ExcessiveOverkill/PCB-business-cards/STM32/opensauce 2024/opensauce2024/Core/Inc/imageData.h

#define IMAGE_DATA {0, 0, 0, 0, 0, 0, 0, 8386560, 8391680, 16778752, 16778752, 16778752, 536870910, 1073741823, 1610612743, 3221225475, 2147483651, 2147483651, 2179989507, 2214068350, 2216427584, 2215379008, 2215379008, 2215379008, 2215379070, 2240544775, 2240544771, 2240544771, 1166802947, 629932035, 495976446, 34078720, 32505856, 0, 0, 0, 0, 0, 0, 0, 0, 7340032, 7340032, 7340032, 25952256, 25952256, 110231552, 110231552, 77692928, 138932224, 135794432, 136315072, 138412080, 138412044, 142606338, 142606337, 83886081, 83886081, 50331649, 16777246, 16777232, 16777232, 16777248, 16777248, 16777248, 16777280, 16777280, 16777280, 8388656, 8388616, 4194312, 3145736, 1015864, 32704, 0, 0, 0, 0, 0, 0, 0, 0, 7340032, 7340032, 7340032, 25952256, 25952256, 110231552, 110231552, 77692928, 142598144, 159415296, 167773056, 201326704, 134217740, 134217730, 268435457, 268435457, 536870913, 536870913, 536870974, 536870944, 536870944, 536870976, 536870976, 536870976, 536871040, 536871040, 268435520, 134217776, 100663304, 25165832, 7340040, 1048568, 0, 0, 0, 0, 0, 0, 0, 0, 0, 7340032, 7340032, 7340032, 25952256, 25952256, 110231552, 110231552, 77660160, 138469376, 134223872, 134219264, 134218112, 134217840, 134217742, 134217729, 71303169, 75497473, 50331649, 33554446, 67108880, 67108896, 134217760, 134217792, 268435520, 268435584, 268435584, 268435584, 268435568, 268435464, 268435464, 268435464, 268435512, 268435648, 134219520, 67115008, 67115008, 33579008, 33579008, 33521664, 33521664, 335216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
#define SECRET_IMAGE_LENGTH 40
#define SECRET_FRAME_LENGTH 40
#define SECRET_FRAME_DISPLAY_CYCLES {2}
#define RANDOM_CHANCE 1
#define RANDOM_POINTS 1
#define SECRET_DISPLAY_CYCLES 1
